tepeka/Gaggia-Upgrade/src/RTD.cpp

#include "RTD.h"

RTD::RTD(short pin) {
  m_rtd = new PWFusion_MAX31865_RTD(pin);

  SPI.begin();                            // begin SPI
  SPI.setClockDivider(SPI_CLOCK_DIV16);   // SPI speed to SPI_CLOCK_DIV16 (1MHz)
  SPI.setDataMode(SPI_MODE1);             // MAX31865 works in MODE1 or MODE3

  pinMode(pin, OUTPUT);
  m_rtd->MAX31865_config();
}

RTD::~RTD() { 
  delete m_rtd;
}


double RTD::ReadTemp()
{
  bool error = false;

  static struct var_max31865 RTD_CH0;
  RTD_CH0.RTD_type = 1;

  struct var_max31865 *rtd_ptr;
  rtd_ptr = &RTD_CH0;
  m_rtd->MAX31865_full_read(rtd_ptr);          // Update MAX31855 readings

  if (0 == RTD_CH0.status)
  {
    // calculate RTD temperature (simple calc, +/- 2 deg C from -100C to 100C)
    m_currentTemp = ((double)RTD_CH0.rtd_res_raw / 32) - 256;
  }
  else
  {
    error = true;
    if (0x80 & RTD_CH0.status)
    {
      // RTD high threshold fault
      if (Serial.available()) Serial.println(F("RTD High Threshold Met"));  
    }
    else if (0x40 & RTD_CH0.status)
    {
      // RTD low threshold fault
      if (Serial.available()) Serial.println(F("RTD Low Threshold Met"));  
    }
    else if (0x20 & RTD_CH0.status)
    {
      // REFin- > 0.85 x Vbias
      if (Serial.available()) Serial.println(F("REFin- > 0.85 x Vbias"));  
    }
    else if (0x10 & RTD_CH0.status)
    {
      // REFin- < 0.85 x Vbias, FORCE- open
      if (Serial.available()) Serial.println(F("FORCE- open"));  
    }
    else if (0x08 & RTD_CH0.status)
    {
      // RTDin- < 0.85 x Vbias, FORCE- open
      if (Serial.available()) Serial.println(F("FORCE- open"));  
    }
    else if (0x04 & RTD_CH0.status)
    {
      // overvoltage/undervoltage fault
      if (Serial.available()) Serial.println(F("Over/Under voltage fault"));  
    }
    else
    {
      // print RTD temperature heading
      if (Serial.available()) Serial.println(F("Unknown fault, check connection"));  
    }
  }
  return m_currentTemp;
}
